slebed/KingShroud/docs/shrouds/assets/InsertLastLED.jpg

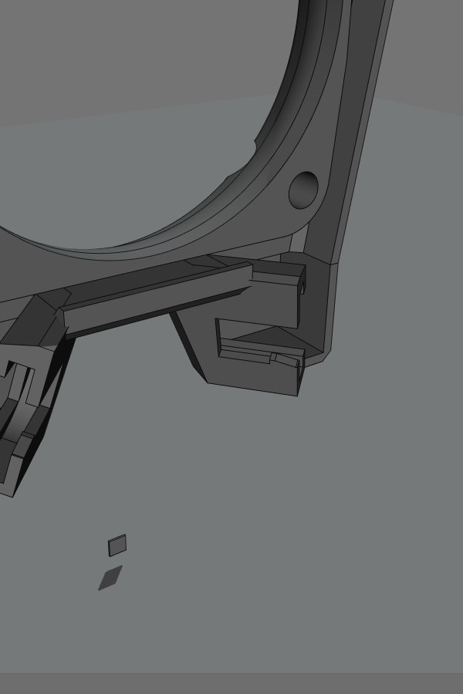
docs/shrouds/assets/InsertLastLED.jpg
