slebed/KingShroud/docs/shrouds/assets/photo_KS_ADXLport.jpg

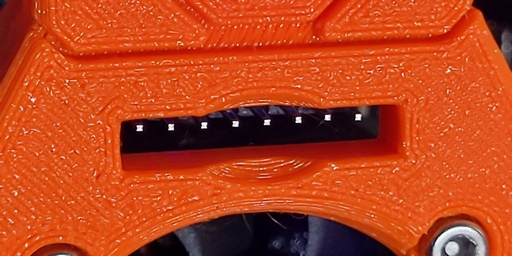
docs/shrouds/assets/photo_KS_ADXLport.jpg
