slebed/KingShroud/docs/shrouds/assets/photo_wired1.jpg

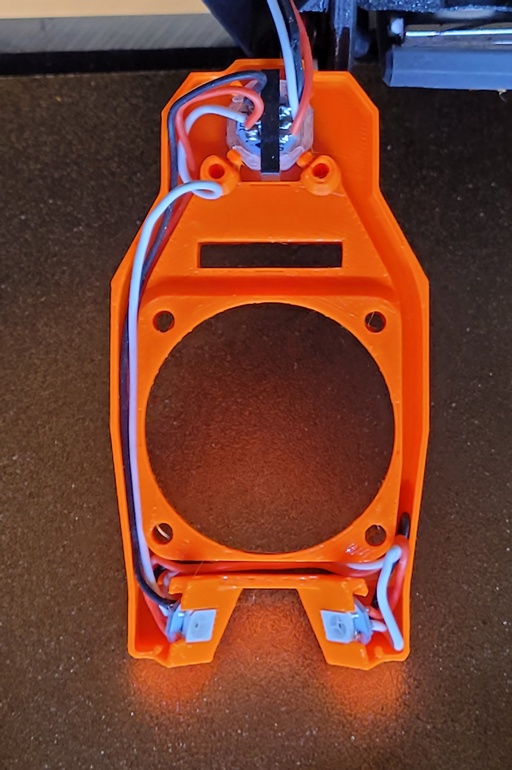
docs/shrouds/assets/photo_wired1.jpg
