slebed/KingShroud/docs/shrouds/assets/photo_wired.jpg

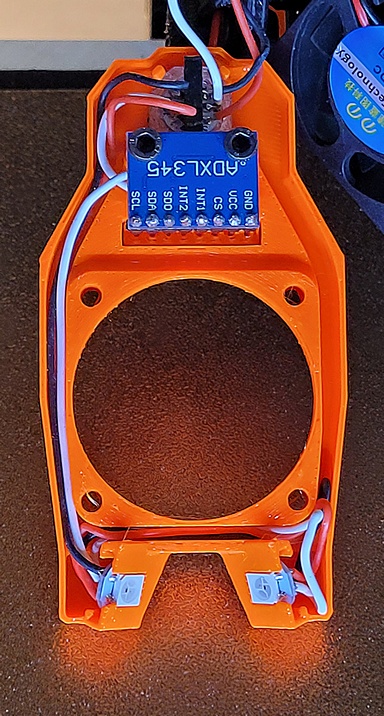
docs/shrouds/assets/photo_wired.jpg
